michalmonday/sim_racing_arduino_controller/images/20240514_150718.jpg

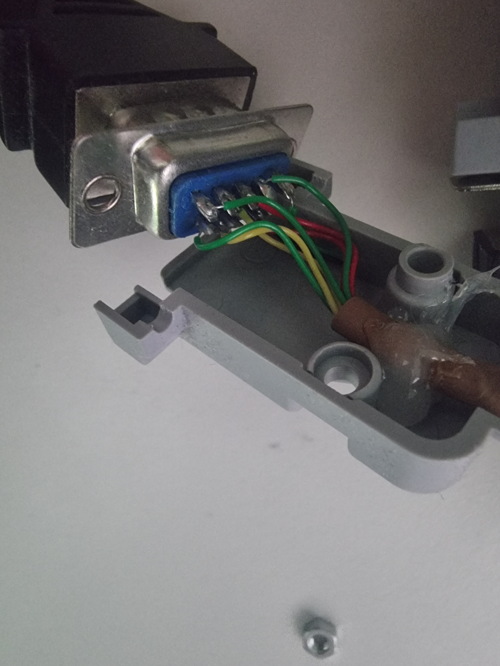
images/20240514_150718.jpg
